machmar/Circad-n-rhythms-/wiki files/flashing/confirmation.png

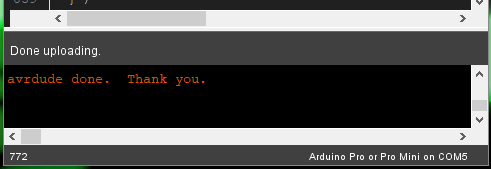
wiki files/flashing/confirmation.png
