machmar/Circad-n-rhythms-/wiki files/flashing/upload.png

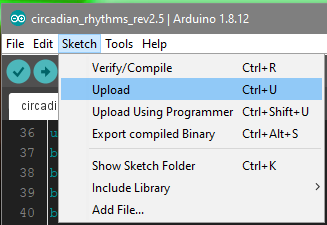
wiki files/flashing/upload.png
